Maulik176/MASC-213/Photos/Photo4.jpeg

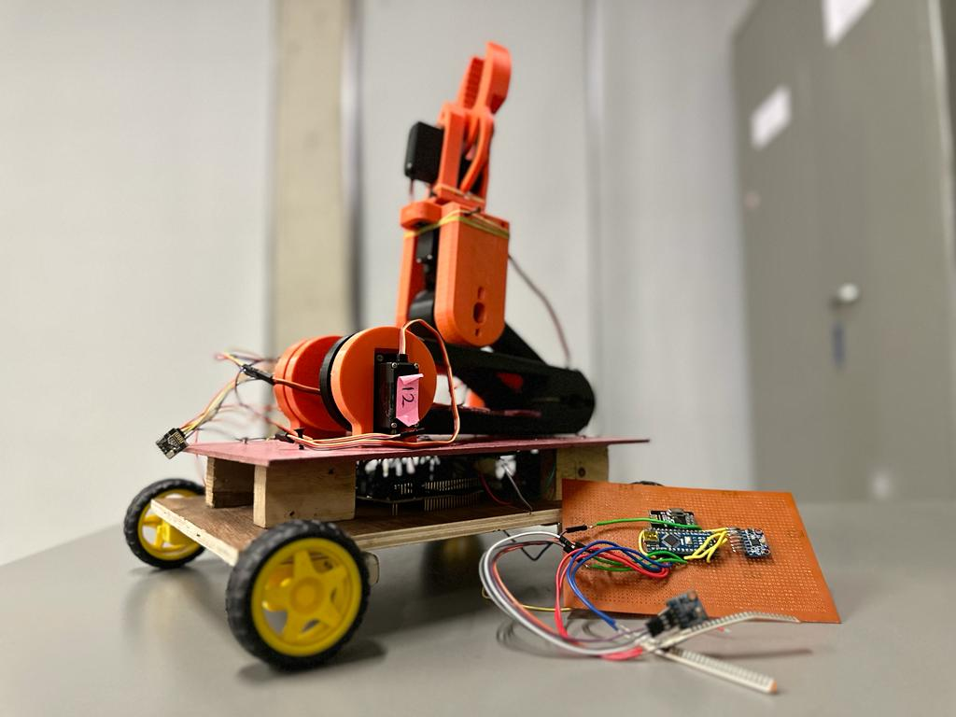
Photos/Photo4.jpeg
