Maulik176/MASC-213/Photos/Photo1.jpeg

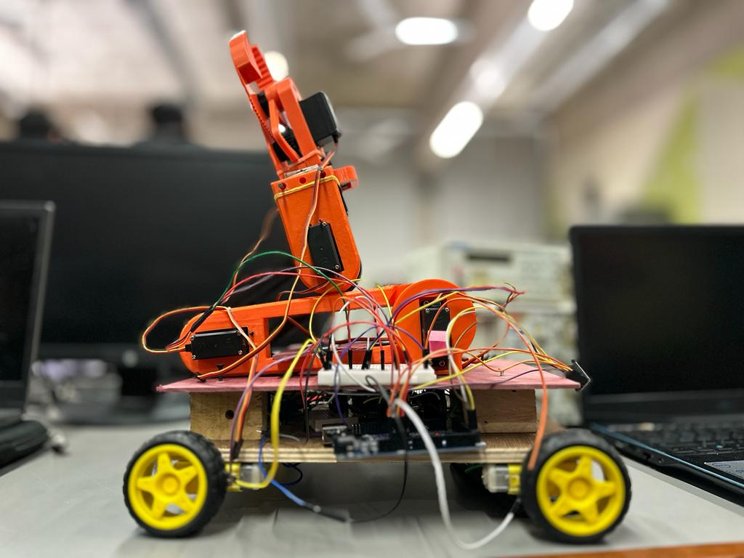
Photos/Photo1.jpeg
