Maulik176/MASC-213/Photos/Photo2.jpeg

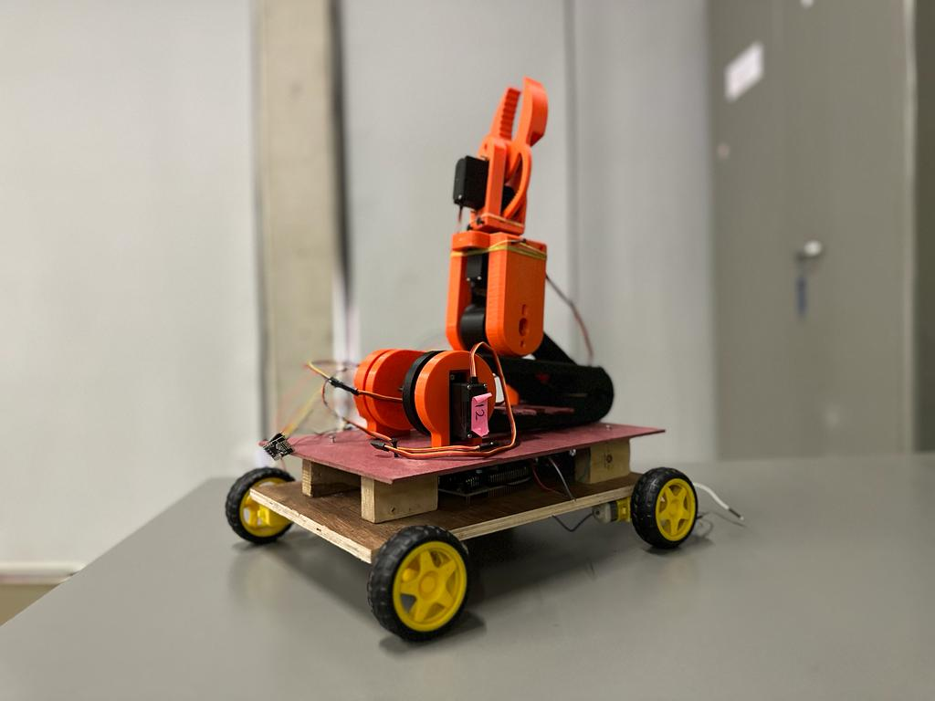
Photos/Photo2.jpeg
