Maulik176/MASC-213/Photos/Photo3.jpeg

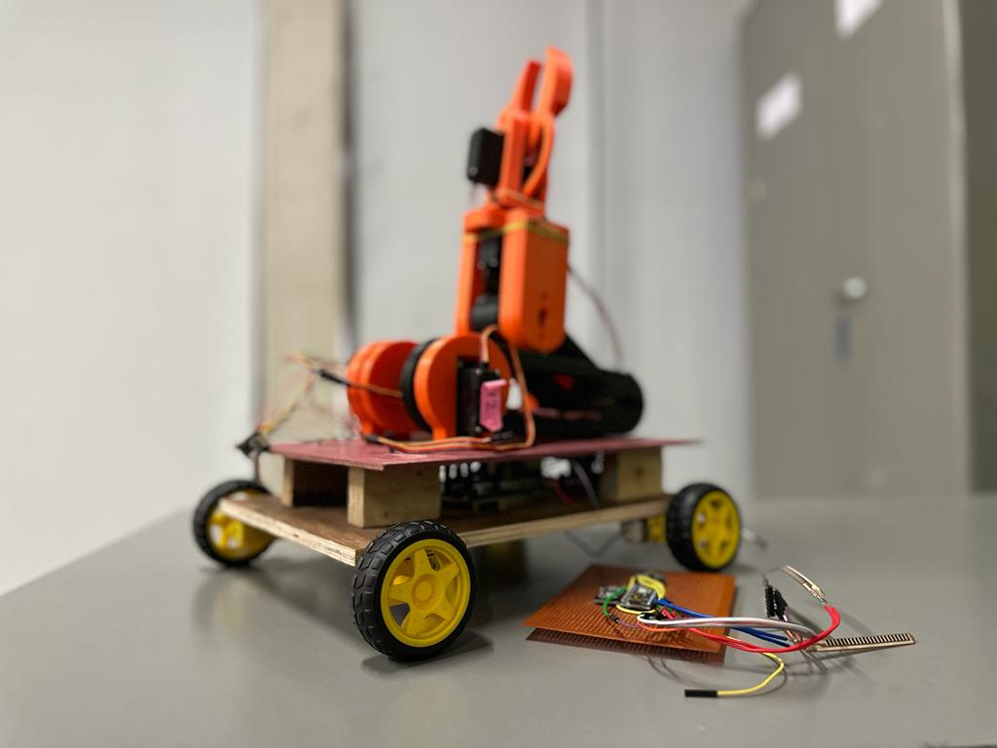
Photos/Photo3.jpeg
