Maulik176/MASC-213/Photos/Photo6.jpeg

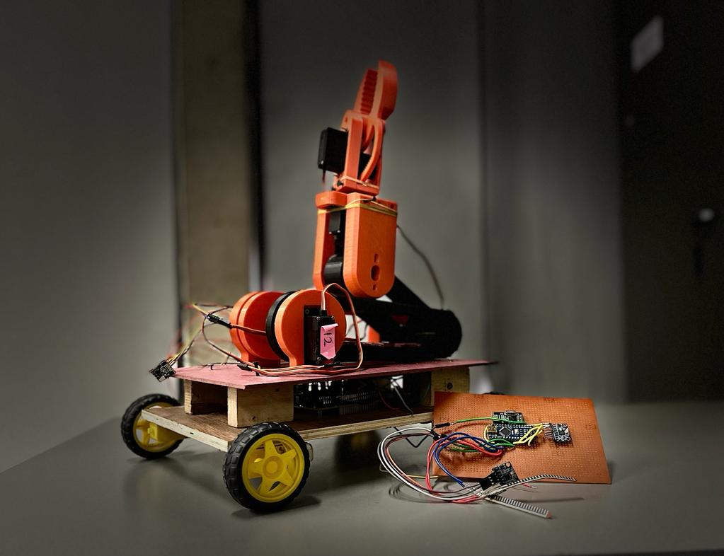
Photos/Photo6.jpeg
