Maulik176/MASC-213/STL_Files/Bearing_guide.STL

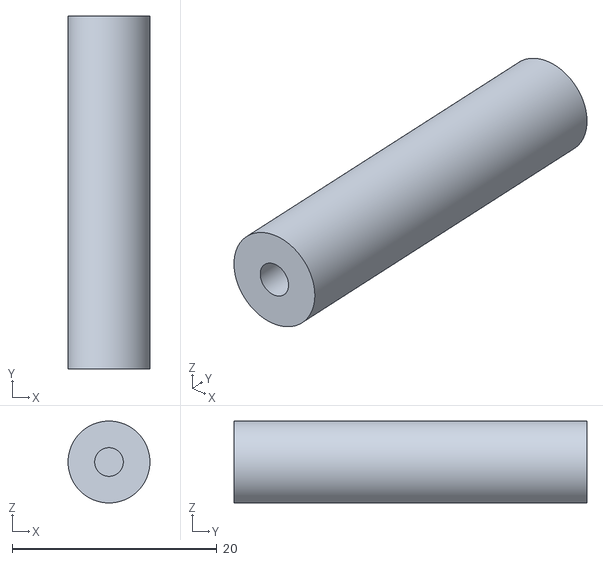
[picture p24: CAD file, 2022-12-16]
STL_Files/Bearing_guide.STL
8.00 x 34.5 x 8.00
