Maulik176/MASC-213/STL_Files/Cover_plate.STL

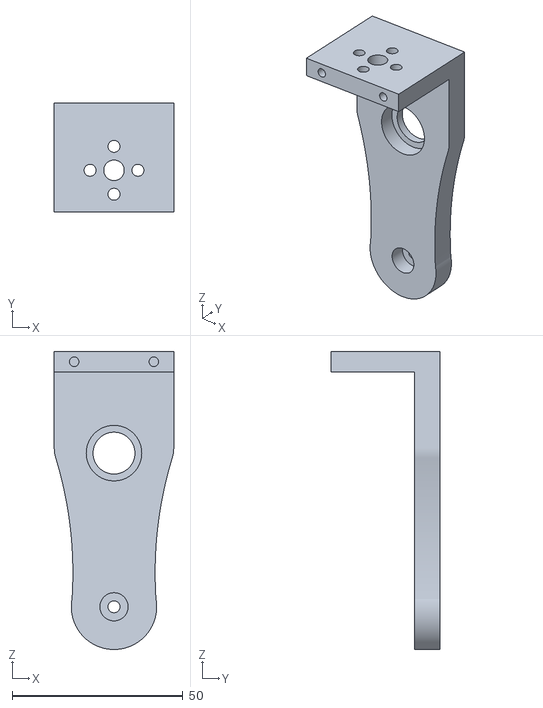
[picture p25: CAD file, 2022-12-16]
STL_Files/Cover_plate.STL
35.0 x 32.0 x 87.2
