Maulik176/MASC-213/STL_Files/Lower_arm_bushing.STL

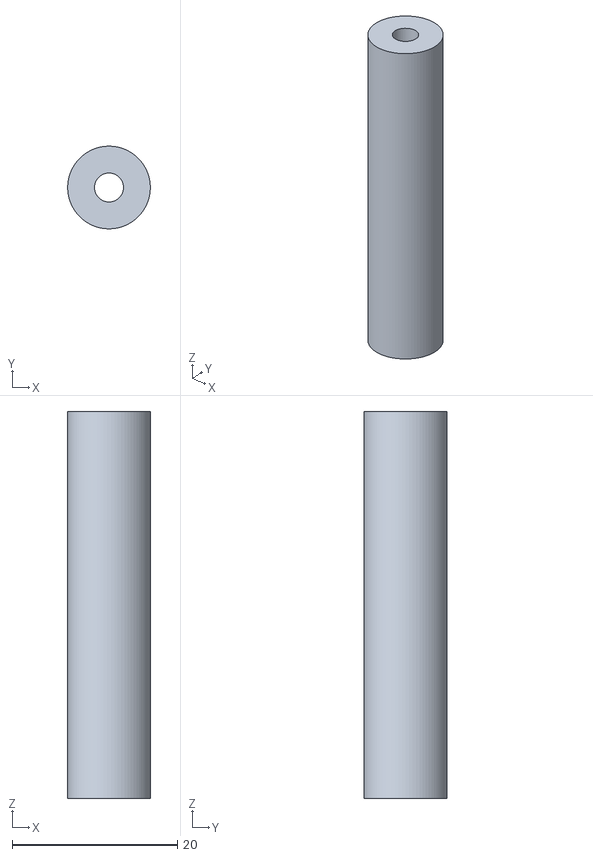
[picture p26: CAD file, 2022-12-16]
STL_Files/Lower_arm_bushing.STL
10.0 x 9.99 x 46.8
