Maulik176/MASC-213/base_dc_motor/Core/Src/main.c

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
/* Includes ------------------------------------------------------------------*/
#include "main.h"

/* USER CODE BEGIN Includes */
#include "string.h"
#include "stdlib.h"
/* USER CODE END Includes */

I2C_HandleTypeDef hi2c1;

TIM_HandleTypeDef htim1;

UART_HandleTypeDef huart2;

/* USER CODE BEGIN PV */
int speed =0;
/* USER CODE END PV */

void SystemClock_Config(void);
static void MX_GPIO_Init(void);
static void MX_I2C1_Init(void);
static void MX_TIM1_Init(void);
static void MX_USART2_UART_Init(void);
/* USER CODE BEGIN 0 */
	uint8_t rxbuffer[13];
	char x[5];
	char y[4];
	char state;
	int val1;
	int val2;
	int flag=0;
	int i=0,j=-1,k=-1,l=-1;
/* USER CODE END 0 */

/**
  * @brief  The application entry point.
  * @retval int
  */
int main(void)
{
  /* MCU Configuration--------------------------------------------------------*/

  /* Reset of all peripherals, Initializes the Flash interface and the Systick. */
  HAL_Init();

  /* Configure the system clock */
  SystemClock_Config();

  /* Initialize all configured peripherals */
  MX_GPIO_Init();
  MX_I2C1_Init();
  MX_TIM1_Init();
  MX_USART2_UART_Init();
  /* USER CODE BEGIN 2 */
	HAL_TIM_PWM_Start(&htim1, TIM_CHANNEL_1);	// Front left
  HAL_TIM_PWM_Start(&htim1, TIM_CHANNEL_2);	// Front right
	HAL_TIM_PWM_Start(&htim1, TIM_CHANNEL_3); // Back left
  HAL_TIM_PWM_Start(&htim1, TIM_CHANNEL_4);	// Back right
	
	HAL_GPIO_WritePin(GPIOA, GPIO_PIN_4, 0);	// Front left
	HAL_GPIO_WritePin(GPIOA, GPIO_PIN_5, 0);	// Front left
  HAL_GPIO_WritePin(GPIOA, GPIO_PIN_6, 0);  // Front right
  HAL_GPIO_WritePin(GPIOA, GPIO_PIN_7, 0);	// Front right
	HAL_GPIO_WritePin(GPIOB, GPIO_PIN_0, 0);	// Back left
	HAL_GPIO_WritePin(GPIOB, GPIO_PIN_1, 0);	// Back left
	HAL_GPIO_WritePin(GPIOC, GPIO_PIN_4, 0);	// Back right
	HAL_GPIO_WritePin(GPIOC, GPIO_PIN_5, 0);	// Back right
  /* USER CODE END 2 */

  /* Infinite loop */
  /* USER CODE BEGIN WHILE */
  while (1)
  {
		
	////////////////////////////////////////////////////////
		
		HAL_I2C_Master_Receive(&hi2c1, (4<<1), (uint8_t *)rxbuffer,13,100);  //Receive data from arduino using I2C
		
		HAL_UART_Transmit(&huart2,rxbuffer,13,100);
		
		i=0;
		j=-1;
		k=-1;
		
		for(i=0; i<13; i++)
		{
			if(rxbuffer[i]==',')
      {
				flag++;
      }
      else if(flag==0)
      {
				j++;
				x[j]=rxbuffer[i];
      }
      else if(flag==1)
      {
				k++;
        y[k]=rxbuffer[i];
      }
			
		}
		flag = 0;
		
		val1 = atoi(x);
		val2 = atoi(y);
		
		if(val1==0 && val2==0)
		{
			speed = 0;
			__HAL_TIM_SET_COMPARE(&htim1,TIM_CHANNEL_1, speed);
			__HAL_TIM_SET_COMPARE(&htim1,TIM_CHANNEL_2, speed);
			__HAL_TIM_SET_COMPARE(&htim1,TIM_CHANNEL_3, speed);
			__HAL_TIM_SET_COMPARE(&htim1,TIM_CHANNEL_4, speed);
		}
		else
		{
			if(val2<340 && val2>270)
		{
			//front
			speed = 1000;
			HAL_GPIO_WritePin(GPIOA, GPIO_PIN_4, 1);	// Front left
			HAL_GPIO_WritePin(GPIOA, GPIO_PIN_5, 0);	// Front left
			__HAL_TIM_SET_COMPARE(&htim1,TIM_CHANNEL_1, speed);
			
			HAL_GPIO_WritePin(GPIOA, GPIO_PIN_6, 1);  // Front right
			HAL_GPIO_WritePin(GPIOA, GPIO_PIN_7, 0);	// Front right
			__HAL_TIM_SET_COMPARE(&htim1,TIM_CHANNEL_2, speed);
			
			HAL_GPIO_WritePin(GPIOB, GPIO_PIN_0, 1);	// Back left
			HAL_GPIO_WritePin(GPIOB, GPIO_PIN_1, 0);	// Back left
			__HAL_TIM_SET_COMPARE(&htim1,TIM_CHANNEL_3, speed);
			
			HAL_GPIO_WritePin(GPIOC, GPIO_PIN_4, 1);	// Back right
			HAL_GPIO_WritePin(GPIOC, GPIO_PIN_5, 0);	// Back right
			__HAL_TIM_SET_COMPARE(&htim1,TIM_CHANNEL_4, speed);
			
		}

		else if(val2<90 && val2>20)
		{
			//back
			speed = 1000;
			HAL_GPIO_WritePin(GPIOA, GPIO_PIN_4, 0);	// Front left
			HAL_GPIO_WritePin(GPIOA, GPIO_PIN_5, 1);	// Front left
			
			HAL_GPIO_WritePin(GPIOA, GPIO_PIN_6, 0);  // Front right
			HAL_GPIO_WritePin(GPIOA, GPIO_PIN_7, 1);	// Front right
			
			HAL_GPIO_WritePin(GPIOB, GPIO_PIN_0, 0);	// Back left
			HAL_GPIO_WritePin(GPIOB, GPIO_PIN_1, 1);	// Back left
			
			HAL_GPIO_WritePin(GPIOC, GPIO_PIN_4, 0);	// Back right
			HAL_GPIO_WritePin(GPIOC, GPIO_PIN_5, 1);	// Back right
			
			__HAL_TIM_SET_COMPARE(&htim1,TIM_CHANNEL_1, speed);
			__HAL_TIM_SET_COMPARE(&htim1,TIM_CHANNEL_2, speed);
			__HAL_TIM_SET_COMPARE(&htim1,TIM_CHANNEL_3, speed);
			__HAL_TIM_SET_COMPARE(&htim1,TIM_CHANNEL_4, speed);
		}
		
		else if(val1<340 && val1>270)
		{
			//left
			speed = 1000;
			HAL_GPIO_WritePin(GPIOA, GPIO_PIN_4, 0);	// Front left
			HAL_GPIO_WritePin(GPIOA, GPIO_PIN_5, 1);	// Front left
			
			HAL_GPIO_WritePin(GPIOA, GPIO_PIN_6, 1);  // Front right
			HAL_GPIO_WritePin(GPIOA, GPIO_PIN_7, 0);	// Front right
			
			HAL_GPIO_WritePin(GPIOB, GPIO_PIN_0, 0);	// Back left
			HAL_GPIO_WritePin(GPIOB, GPIO_PIN_1, 1);	// Back left
			
			HAL_GPIO_WritePin(GPIOC, GPIO_PIN_4, 1);	// Back right
			HAL_GPIO_WritePin(GPIOC, GPIO_PIN_5, 0);	// Back right
			
			__HAL_TIM_SET_COMPARE(&htim1,TIM_CHANNEL_1, speed);
			__HAL_TIM_SET_COMPARE(&htim1,TIM_CHANNEL_2, speed);
			__HAL_TIM_SET_COMPARE(&htim1,TIM_CHANNEL_3, speed);
			__HAL_TIM_SET_COMPARE(&htim1,TIM_CHANNEL_4, speed);
		}
		
		else if(val1<90 && val1>20)
		{
			//right
			speed = 1000;
			HAL_GPIO_WritePin(GPIOA, GPIO_PIN_4, 1);	// Front left
			HAL_GPIO_WritePin(GPIOA, GPIO_PIN_5, 0);	// Front left
			
			HAL_GPIO_WritePin(GPIOA, GPIO_PIN_6, 0);  // Front right
			HAL_GPIO_WritePin(GPIOA, GPIO_PIN_7, 1);	// Front right
			
			HAL_GPIO_WritePin(GPIOB, GPIO_PIN_0, 1);	// Back left
			HAL_GPIO_WritePin(GPIOB, GPIO_PIN_1, 0);	// Back left
			
			HAL_GPIO_WritePin(GPIOC, GPIO_PIN_4, 0);	// Back right
			HAL_GPIO_WritePin(GPIOC, GPIO_PIN_5, 1);	// Back right
			
			__HAL_TIM_SET_COMPARE(&htim1,TIM_CHANNEL_1, speed);
			__HAL_TIM_SET_COMPARE(&htim1,TIM_CHANNEL_2, speed);
			__HAL_TIM_SET_COMPARE(&htim1,TIM_CHANNEL_3, speed);
			__HAL_TIM_SET_COMPARE(&htim1,TIM_CHANNEL_4, speed);
		}
		
		else
		{
			speed = 0;
			__HAL_TIM_SET_COMPARE(&htim1,TIM_CHANNEL_1, speed);
			__HAL_TIM_SET_COMPARE(&htim1,TIM_CHANNEL_2, speed);
			__HAL_TIM_SET_COMPARE(&htim1,TIM_CHANNEL_3, speed);
			__HAL_TIM_SET_COMPARE(&htim1,TIM_CHANNEL_4, speed);
		}
		}
			
		
		
	//////////////////////////////////////////////////////////////////////////////////////
    /* USER CODE END WHILE */

    /* USER CODE BEGIN 3 */
  }
  /* USER CODE END 3 */
}

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
